CalmyJane/MidiHero/pictures/IMG_20230328_153816.jpg

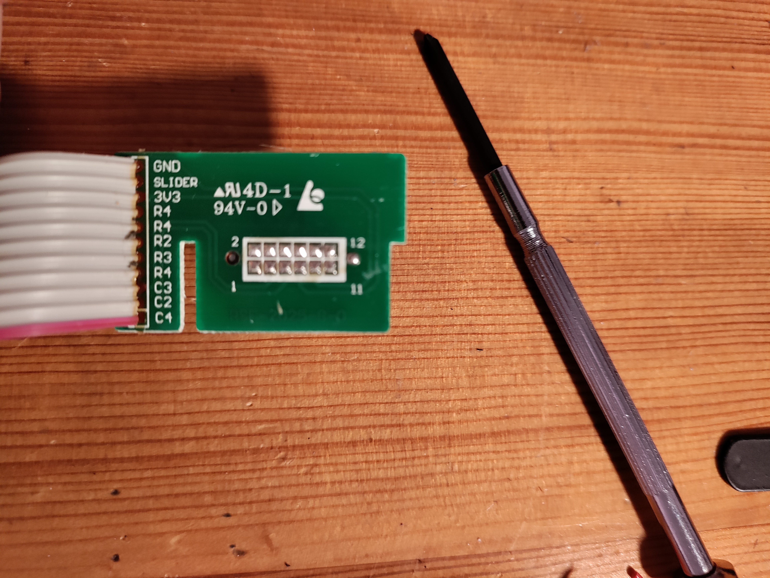
pictures/IMG_20230328_153816.jpg
